mackelec/StepInverter/PCB/Clock_(Eprom)/VER_201811/WarpDrive_201811_2.pdf

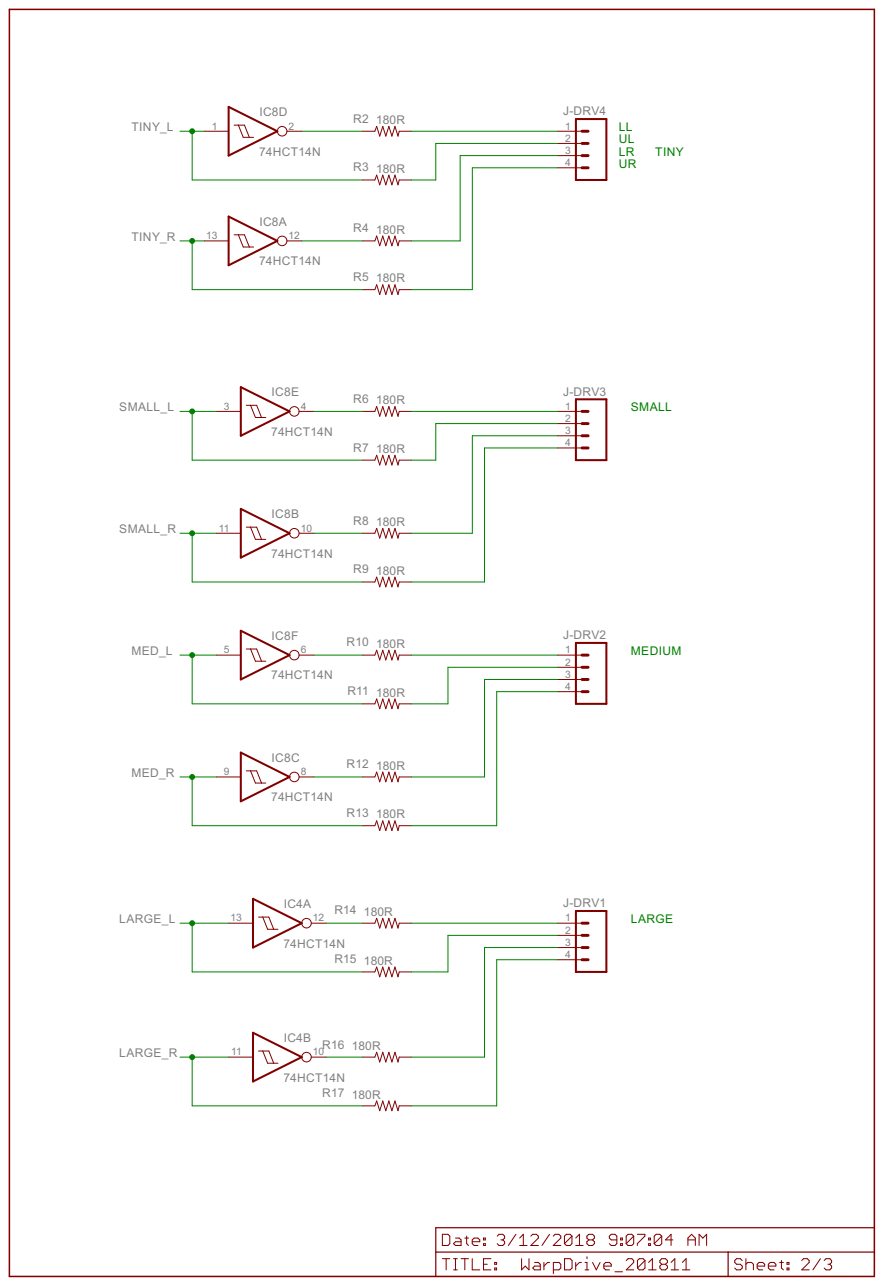
[picture p31: page 1]
