mackelec/StepInverter/PCB/Clock_(Eprom)/VER_201811/WarpDrive_201811_3.pdf

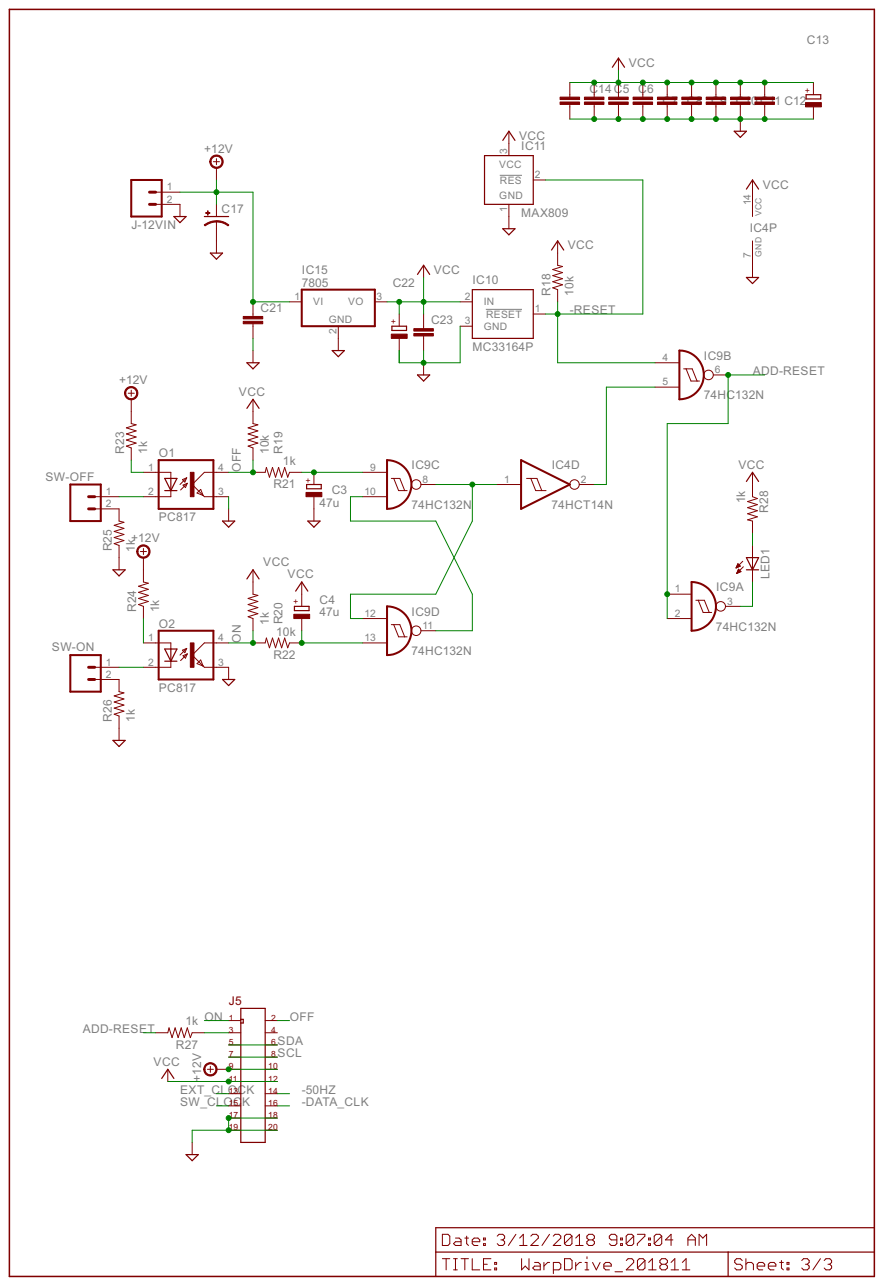
[picture p32: page 1]
