mackelec/StepInverter/stm32WarpVerter/Arduino/stm32_Warpverter/stm32_Warpverter_009/stm32_warpverter_021_LookupTables.ino

#define BATTERY_VOLTAGE_AT_MAX_ADC      180000

#define LOW_DC_VOLT_CUTOFF_ADC      1820
#define HIGH_DC_VOLT_CUTOFF_ADC     4095


#define DC_CURRENT_CUTOFF_ADC        3890
#define FAN1_ON_DC_CURRENT_ADC       2252
#define FAN1_OFF_DC_CURRENT_ADC      2191
#define FAN2_ON_DC_CURRENT_ADC       2355
#define FAN2_OFF_DC_CURRENT_ADC      2293

#define TEMPERATURE_1_ADC_SHUTDOWN    3464
#define TEMPERATURE_2_ADC_SHUTDOWN    3644

#define FAN1_ADC_TURNON    0
#define FAN1_ADC_TURNOFF   0
#define FAN2_ADC_TURNON    3225
#define FAN2_ADC_TURNOFF   2918

int16 flash_sineLookup[]  __FLASH__ = { 0,20,41,61,82,102,123,143,164,184
                   ,205,225,246,266,286,307,327,348,368,388
                   ,409,429,449,469,490,510,530,550,571,591
                   ,611,631,651,671,691,711,731,751,771,791
                   ,811,831,851,870,890,910,930,949,969,988
                   ,1008,1027,1047,1066,1086,1105,1124,1144,1163,1182
                   ,1201,1220,1239,1258,1277,1296,1315,1334,1353,1371
                   ,1390,1408,1427,1445,1464,1482,1501,1519,1537,1555
                   ,1573,1591,1609,1627,1645,1663,1681,1698,1716,1733
                   ,1751,1768,1786,1803,1820,1837,1854,1871,1888,1905
                   ,1922,1938,1955,1972,1988,2005,2021,2037,2053,2069
                   ,2085,2101,2117,2133,2149,2164,2180,2195,2211,2226
                   ,2241,2256,2272,2286,2301,2316,2331,2345,2360,2374
                   ,2389,2403,2417,2431,2445,2459,2473,2487,2500,2514
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
                   ,0,0,0,0,0,0,0,0,0,0,0,0,0,0,0,0,0
                   ,0,0,0,0,0,0,0,0,0,0,0,0,0,0,0,0,0
                   ,0,0,0,0,0,0,0,0,0,0,0,0,0,0,0,0,0
                   ,0,0,0,0,0,0,0,0,0,0,0,0,0,0,0,0,0
                   ,0,0,0,0,0,0,0,0,0,0,0,0,0,0,0,0,0
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
