mackelec/StepInverter/stm32WarpVerter/Arduino/stm32_Warpverter/stm32_Warpverter_009/stm32_warpverter_030_setup.ino

void setup() 
{
  afio_cfg_debug_ports(AFIO_DEBUG_NONE);
  Serial.begin(9600);
  
  pinMode(pin50Hz,OUTPUT);
  pinMode(PB3,OUTPUT);      // test pin  : toggles on timer
  pinMode(PB5,OUTPUT);      // test pin
  pinMode(PB4,OUTPUT);      // test pin 
  pinMode(PA15,OUTPUT);      // test pin 

  pinMode(adcPinI,INPUT_ANALOG);
  pinMode(PIN_THERM1,INPUT_ANALOG);
  pinMode(PIN_THERM2,INPUT_ANALOG);
  pinMode(PIN_VAC,INPUT_ANALOG);
  pinMode(PIN_IAC,INPUT_ANALOG);
  
  

  pinMode(LED,OUTPUT);
  //slow way
  pinMode(PB8,OUTPUT);
  pinMode(PB9,OUTPUT);
  pinMode(PB10,OUTPUT);
  pinMode(PB11,OUTPUT);
  pinMode(PB12,OUTPUT);
  pinMode(PB13,OUTPUT);
  pinMode(PB14,OUTPUT);
  pinMode(PB15,OUTPUT);

  pinMode(pinSwOff,INPUT_PULLUP);
  pinMode(pinSwON,INPUT_PULLUP);
  pinMode(PIN_SYNCINP,INPUT_PULLUP);

  pinMode(pinFAN1,PWM);
  pinMode(pinFAN2,PWM);
  analogWrite(pinFAN1,0);
  analogWrite(pinFAN2,0);
  pinMode(pinRelay,OUTPUT);

  bool tablesCheck = checkTables();
  Serial.flush();
  //---   BluePill onboard LED is turned by writing LOW 
  //        opposite of most arduino boards  
  digitalWrite(LED,LOW);
  delay(1000);
  
  // quick way, the upper 8 bits all set to output, pushpull
  GPIOB->regs->CRH = 0x33333333;
  GPIOB->regs->ODR = 0;

  if (USE_FIXED_BATTERY_VOLTAGE > 0)
  {
    float x = (USE_FIXED_BATTERY_VOLTAGE * 4096.0)/ BATTERY_VOLTAGE_AT_MAX_ADC + 0.5;
    adcFixedVoltage = int(x);
  }

/*-----------------------------------------------
 *  
 *      ADC setup
 *      
 *      -  STM32F103 has dual ADCs 
 *           ADC2 reads Battery Voltage
 *           ADC1 is used in scan mode, multiplexed, 
 *             reads Thermistor 1 & 2, Battery Current, AC voltage and Current 
 *      -  ADC 1 & 2 are set in continuous conversion modeso we don't waste time servicing it.
 *      -  ADC1 is using DMA into a 5 element buffer.
 *      -  Using the the same scan rate as in the powerScope so it is faster than 6400Hz
 *      
 *  
 ------------------------------------------------*/

  adcV.calibrate();
  adcV.setSampleRate(ADC_SMPR_239_5);
  adcV.setPins(&adcPinV, 1);
  adcV.setContinuous();

  adc_2.calibrate();
  adc_2.setSampleRate(ADC_SMPR_239_5);//set the Sample Rate
  adc_2.setScanMode();              
  adc_2.setPins(analogInputs, 5);   //set how many and which pins to convert.
  adc_2.setContinuous();            //set the ADC in continuous mode.

//set the DMA transfer for the ADC. 
//in this case we want to increment the memory side and run it in circular mode
//By doing this, we can read the last value sampled from the channels by reading the dataPoints array
  adc_2.setDMA(adcData, 5, (DMA_MINC_MODE | DMA_CIRC_MODE), NULL);

  adcV.startConversion();
  adc_2.startConversion();
  
  
  //*******  Timer setup  ( 19.52777777777777777778 microseconds, 51209.10384068278805121 Hz)
  //---  output Frquency = 50.00889046941678520626 Hz
  //---  inverterTimer frequency = 51200Hz (50Hz x 1024 steps)
  //---  inverterTimer period = 19.53125 uSec
  //---  overflow = 72MHz / 51200Hz = 1406.25
  
  inverterTimer.setMode(TIMER_CH4, TIMER_OUTPUT_COMPARE);
  inverterTimer.pause();
  inverterTimer.setPrescaleFactor(1);//1
  inverterTimer.setCount(0);
  inverterTimer.setOverflow(TIMER_OVERFLOW);//1406
  inverterTimer.setCompare(TIMER_CH4, 1);  
  inverterTimer.attachCompare4Interrupt(timer_Handler);
  inverterTimer.refresh();
  
  delay(1000);
  Serial << "stm32-StepInverter  Setup done" << endl;
  Serial.flush();

   //--- Starting with Inverter running for testing purposes.
   //---   I prefer Inverter NOT  running on start-up in real use.
  shutDown();    // 
  //digitalWrite(LED,HIGH);  // uncomment if startup with inverter off


  // mains sync
  p_lock = 0;          // phase lock flag = 0 = NOT locked
  pcount_acc = 0;      // fractional integer math. Each PWM, pcount_delta is added to pcount_acc and divided by 1024
  pcount_delta = 1024; // in effect we are getting an addition of 1. But pcount_delta can be modified, a little bigger or smaller..
  old_phase_error = 0; // used in PID, to obtain derivative
  int_f = 0;            // flag used to allow one and only one interrupt, near a zero crossing of AC output
  p_lock = 0;           // use this to tell if phase lock is present or not
  attachInterrupt(PA1,mains_sync,FALLING);

  avgADC_I = adcValueI*128;
  adcRead();
  avgADC_V = adcValueV*128;
  avgADC_VV = avgADC_V;
  avgADC_II = avgADC_I;
  inverterTimer.resume();

}


/*------------------------------------------------------------
 * 
 *      CheckTables : Checks the size of the in - flash arrays
 *      
 *                    -  View the report on Serial Monitor
 *                       after pasting the array data.
 * 
 ------------------------------------------------------------*/

bool checkTables()
{
  int Vsize = sizeof(flash_voltMaskTable);
  int sineSize = sizeof(flash_sineLookup)/2;
  int sizeIF = sizeof(flash_inputFactorTable);
  int sizeCF = sizeof(flash_currentFactorTable);
  bool result = true;
  Serial << endl;
  Serial.flush();
  
  Serial << "checking Table sizes" <<  endl;
  Serial.flush();
  delay(1000);
  Serial << "voltMaskTable size = " ;
  Serial.flush();
  delay(900);
  Serial << Vsize;
  if (Vsize == 0x2000) {Serial << " -- Good " << endl; } else {Serial << "  -- Fail" << endl;result = false;}
  Serial.flush();
  delay(500);
  Serial << "sineLookup size = " << sineSize;
  if (sineSize == STEPS) {Serial << " -- Good " << endl; } else {Serial << "  -- Fail" << endl;result = false;}
  Serial.flush();
  delay(500);
  #ifdef THEFACTORTABLE
    int sizePF = sizeof(flash_TheFactorTable);
    Serial << "The FactorTable size = " << sizePF;
    if (sizePF == 0x10000) {Serial << " -- Good " << endl; } else {Serial << "  -- Fail" << endl;result = false;}
    Serial.flush();
  #else
    Serial << "inputFactorTable size = " << sizeIF;
    if (sizeIF == 0x1000) {Serial << " -- Good " << endl; } else {Serial << "  -- Fail" << endl;result = false;}
    Serial.flush();
    delay(500);
    Serial << "currentFactorTable size = " << sizeCF;
    if (sizeCF == 0x1000) {Serial << " -- Good " << endl; } else {Serial << "  -- Fail" << endl;result = false;}
    Serial.flush();
  #endif
  return (result);
   
}
