mackelec/StepInverter/stm32WarpVerter/Arduino/stm32_Warpverter/stm32_Warpverter_009/stm32_warpverter_022_theFactor.ino

//#define THEFACTORTABLE 1

uint8 flash_TheFactorTable[]  __FLASH__ = { 
                    0,0,0,0,0,0,0,0,0,0,0,0,0,0,0,0
                   ,0,0,0,0,0,0,0,0,0,0,0,0,0,0,0,0
                   ,0,0,0,0,0,0,0,0,0,0,0,0,0,0,0,0
                   ,0,0,0,0,0,0,0,0,0,0,0,0,0,0,0,0
                   ,0,0,0,0,0,0,0,0,0,0,0,0,0,0,0,0
                   ,0,0,0,0,0,0,0,0,0,0,0,0,0,0,0,0
                   ,0,0,0,0,0,0,0,0,0,0,0,0,0,0,0,0
                   ,0,0,0,0,0,0,0,0,0,0,0,0,0,0,0,0
                   ,0,0,0,0,0,0,0,0,0,0,0,0,0,0,0,0
                   ,0,0,0,0,0,0,0,0,0,0,0,0,0,0,0,0
                   ,0,0,0,0,0,0,0,0,0,0,0,0,0,0,0,0
                   ,0,0,0,0,0,0,0,0,0,0,0,0,0,0,0,0
                   ,0,0,0,0,0,0,0,0,0,0,0,0,0,0,0,0
                   ,0,0,0,0,0,0,0,0,0,0,0,0,0,0,0,0
                   ,0,0,0,0,0,0,0,0,0,0,0,0,0,0,0,0
                   ,0,0,0,0,0,0,0,0,0,0,0,0,0,0,0,0
                   ,0,0,0,0,0,0,0,0,0,0,0,0,0,0,0,0
                   ,0,0,0,0,0,0,0,0,0,0,0,0,0,0,0,0
                   ,0,0,0,0,0,0,0,0,0,0,0,0,0,0,0,0
                   ,0,0,0,0,0,0,0,0,0,0,0,0,0,0,0,0
                   ,0,0,0,0,0,0,0,0,0,0,0,0,0,0,0,0
                   ,0,0,0,0,0,0,0,0,0,0,0,0,0,0,0,0
                   ,0,0,0,0,0,0,0,0,0,0,0,0,0,0,0,0
                   ,0,0,0,0,0,0,0,0,0,0,0,0,0,0,0,0
                   ,0,0,0,0,0,0,0,0,0,0,0,0,0,0,0,0
                   ,0,0,0,0,0,0,0,0,0,0,0,0,0,0,0,0
                   ,0,0,0,0,0,0,0,0,0,0,0,0,0,0,0,0
                   ,0,0,0,0,0,0,0,0,0,0,0,0,0,0,0,0
                   ,0,0,0,0,0,0,0,0,0,0,0,0,0,0,0,0
                   ,0,0,0,0,0,0,0,0,0,0,0,0,0,0,0,0
                   ,0,0,0,0,0,0,0,0,0,0,0,0,0,0,0,0
                   ,0,0,0,0,0,0,0,0,0,0,0,0,0,0,0,0
                   ,0,0,0,0,0,0,0,0,0,0,0,0,0,0,0,0
                   ,0,0,0,0,0,0,0,0,0,0,0,0,0,0,0,0
                   ,0,0,0,0,0,0,0,0,0,0,0,0,0,0,0,0
                   ,0,0,0,0,0,0,0,0,0,0,0,0,0,0,0,0
                   ,0,0,0,0,0,0,0,0,0,0,0,0,0,0,0,0
                   ,0,0,0,0,0,0,0,0,0,0,0,0,0,0,0,0
                   ,0,0,0,0,0,0,0,0,0,0,0,0,0,0,0,0
                   ,0,0,0,0,0,0,0,0,0,0,0,0,0,0,0,0
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
