mackelec/StepInverter/stm32WarpVerter/Arduino/stm32_Warpverter/stm32_Warpverter_ver_007/stm32_warpverter_021_LookupTables.ino

//#define XFACTOR      31005000

#define LOWVOLT_CUTOFF_ADC      2867
#define TEMPERATURE_1_ADC_SHUTDOWN    3463
#define TEMPERATURE_2_ADC_SHUTDOWN    3352



int16 flash_sineLookup[]  __FLASH__ = { 0,21,42,62,83,104,125,146,167,187
                   ,208,229,250,270,291,312,333,353,374,395
                   ,415,436,457,477,498,519,539,560,580,601
                   ,621,642,662,683,703,723,744,764,784,804
                   ,825,845,865,885,905,925,945,965,985,1005
                   ,1025,1045,1065,1084,1104,1124,1143,1163,1183,1202
                   ,1222,1241,1260,1280,1299,1318,1337,1356,1375,1394
                   ,1413,1432,1451,1470,1489,1507,1526,1545,1563,1582
                   ,1600,1618,1637,1655,1673,1691,1709,1727,1745,1763
                   ,1781,1798,1816,1833,1851,1868,1886,1903,1920,1937
                   ,1954,1971,1988,2005,2022,2039,2055,2072,2088,2105
                   ,2121,2137,2153,2169,2185,2201,2217,2233,2248,2264
                   ,2279,2295,2310,2325,2340,2355,2370,2385,2400,2415
                   ,2429,2444,2458,2472,2487,2501,2515,2529,2543,2556
                   ,2570,2584,2597,2610,2624,2637,2650,2663,2676,2688
                   ,2701,2714,2726,2739,2751,2763,2775,2787,2799,2810
                   ,2822,2834,2845,2856,2868,2879,2890,2900,2911,2922
                   ,2932,2943,2953,2963,2973,2983,2993,3003,3013,3022
                   ,3032,3041,3050,3059,3068,3077,3086,3094,3103,3111
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
                   ,0,0,0,0,0,0,0,0,0,0,0,0,0,0,0,0,0
                   ,0,0,0,0,0,0,0,0,0,0,0,0,0,0,0,0,0
                   ,0,0,0,0,0,0,0,0,0,0,0,0,0,0,0,0,0
                   ,0,0,0,0,0,0,0,0,0,0,0,0,0,0,0,0,0
                   ,0,0,0,0,0,0,0,0,0,0,0,0,0,0,0,0,0
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
